KyomaHooin/Wireshield/openscad/schema/bls.jpg

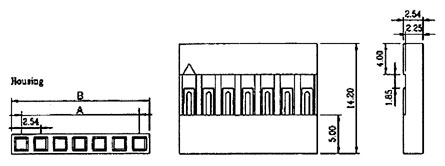
openscad/schema/bls.jpg
