KyomaHooin/Wireshield/openscad/schema/button.jpg

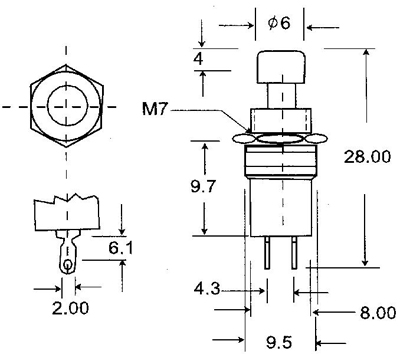
openscad/schema/button.jpg
