KyomaHooin/Wireshield/openscad/schema/idc.jpg

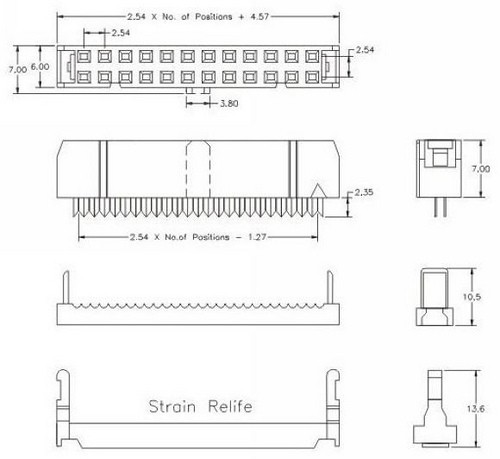
openscad/schema/idc.jpg
