KyomaHooin/Wireshield/openscad/schema/jack.jpg

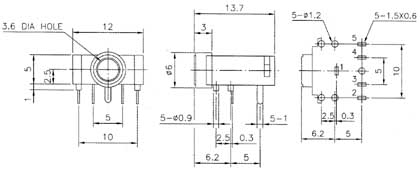
openscad/schema/jack.jpg
