KyomaHooin/Wireshield/openscad/schema/pls.jpg

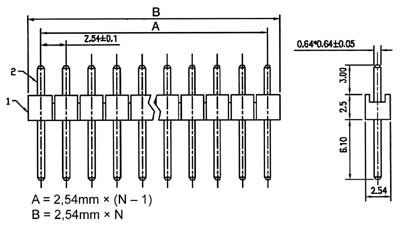
openscad/schema/pls.jpg
