KyomaHooin/Wireshield/openscad/schema/TFT.jpg

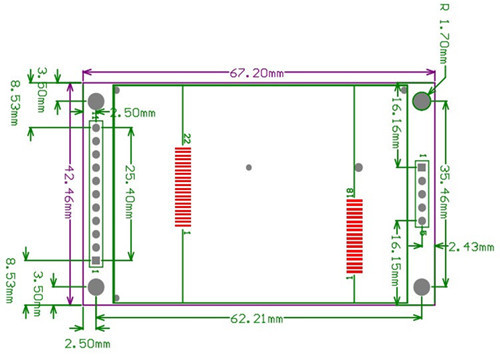
openscad/schema/TFT.jpg
