KyomaHooin/Wireshield/photo/IMG_20170406_092021.jpg

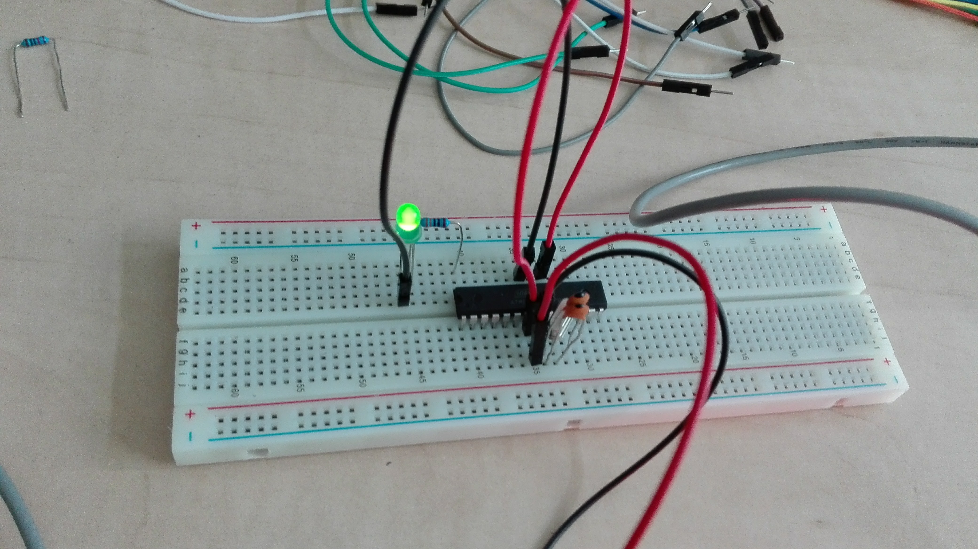
photo/IMG_20170406_092021.jpg
