KyomaHooin/Wireshield/photo/IMG_20170406_093931.jpg

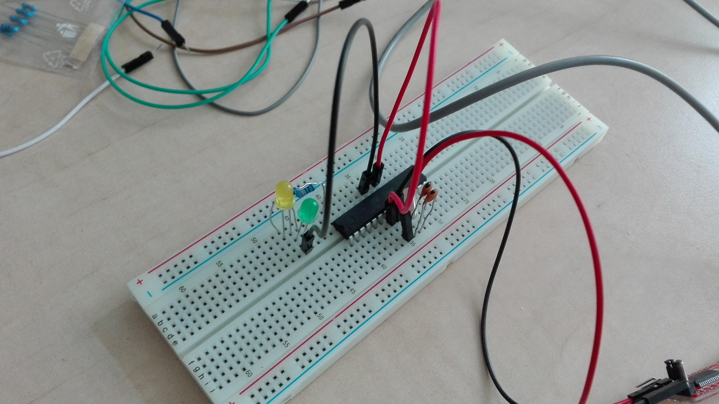
photo/IMG_20170406_093931.jpg
