KyomaHooin/Wireshield/photo/IMG_20170407_105513.jpg

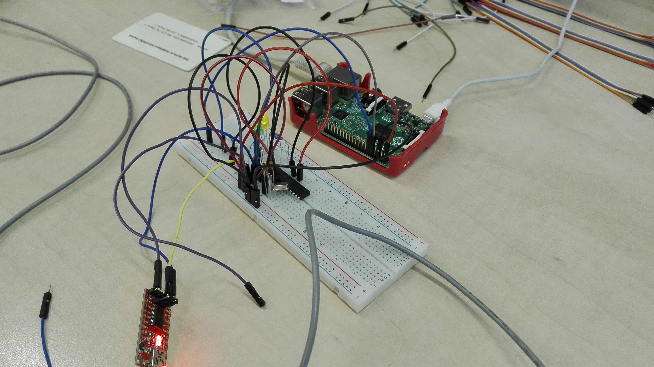
photo/IMG_20170407_105513.jpg
