KyomaHooin/Wireshield/photo/IMG_20170412_122922.jpg

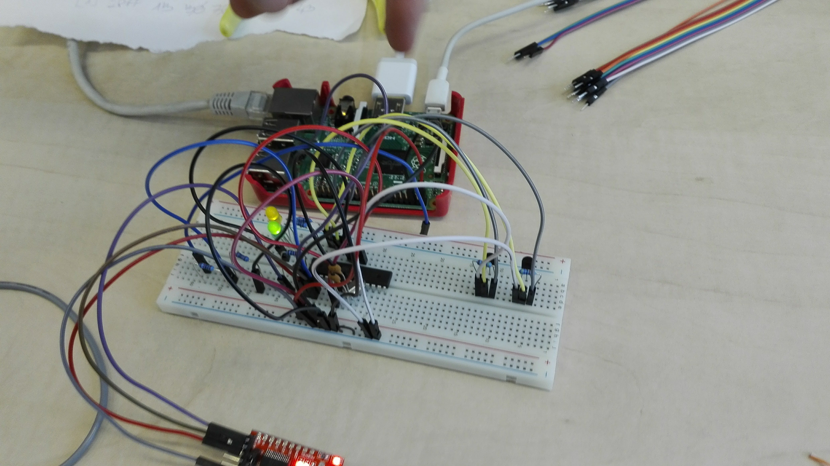
photo/IMG_20170412_122922.jpg
