KyomaHooin/Wireshield/photo/IMG_20170419_115917.jpg

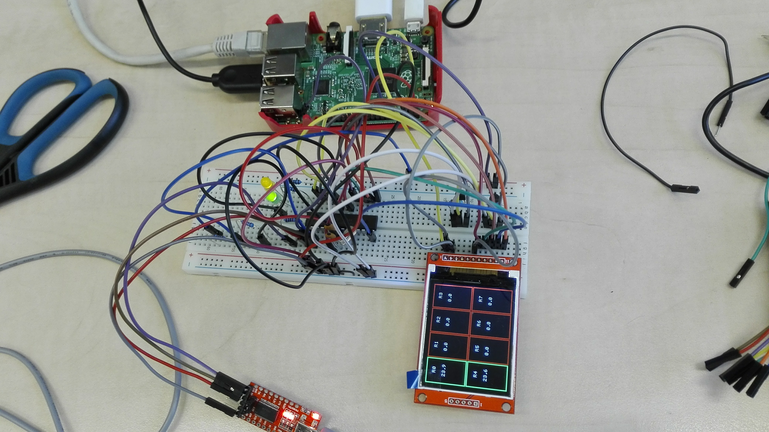
photo/IMG_20170419_115917.jpg
