KyomaHooin/Wireshield/photo/IMG_20170502_114444.jpg

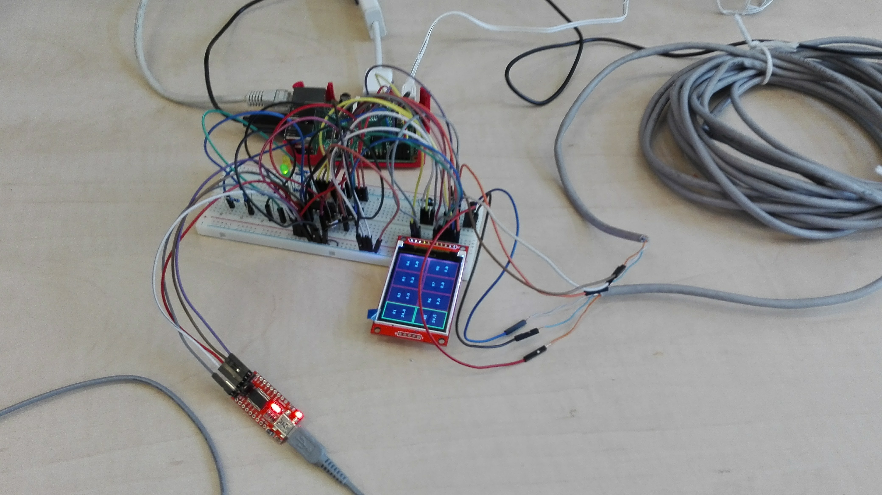
photo/IMG_20170502_114444.jpg
