KyomaHooin/Wireshield/photo/IMG_20170718_132216.jpg

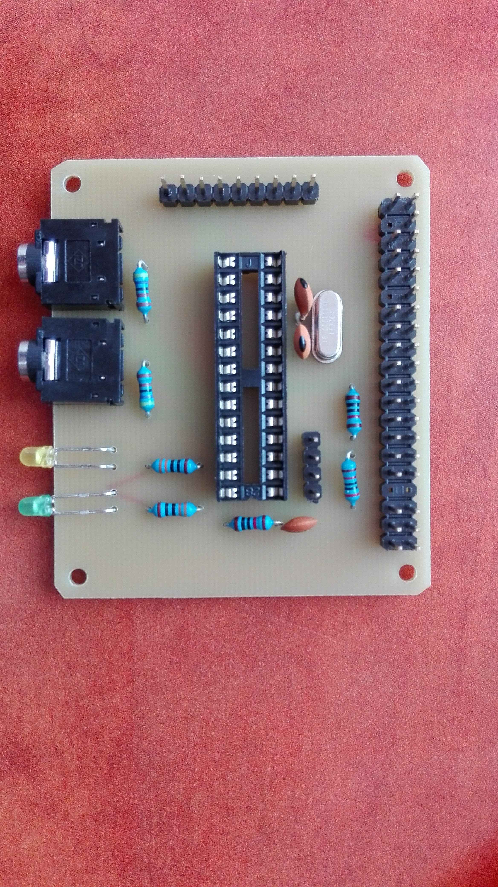
photo/IMG_20170718_132216.jpg
