KyomaHooin/Wireshield/photo/IMG_20170807_113755.jpg

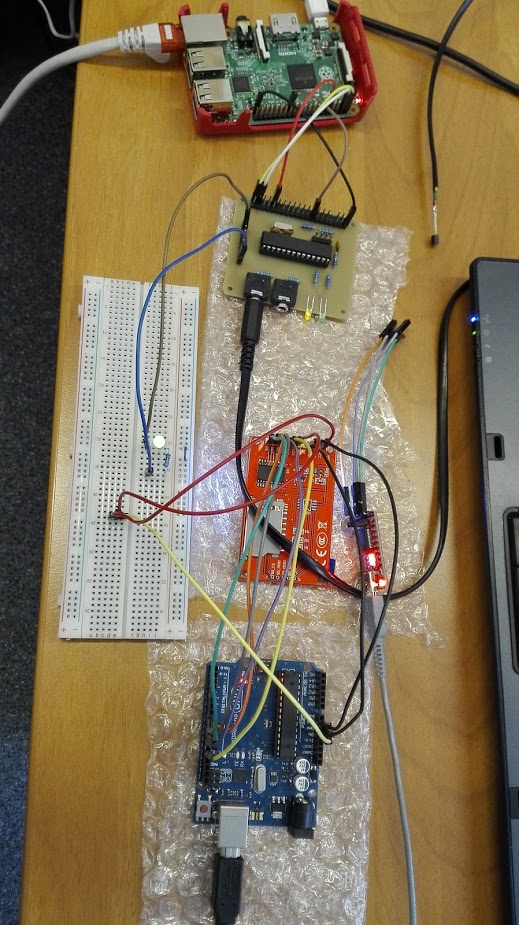
photo/IMG_20170807_113755.jpg
