KyomaHooin/Wireshield/photo/IMG_20170830_094421.jpg

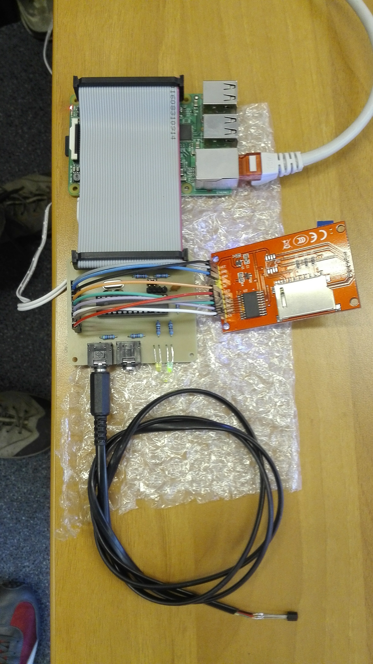
photo/IMG_20170830_094421.jpg
