KyomaHooin/Wireshield/photo/IMG_20170830_094432.jpg

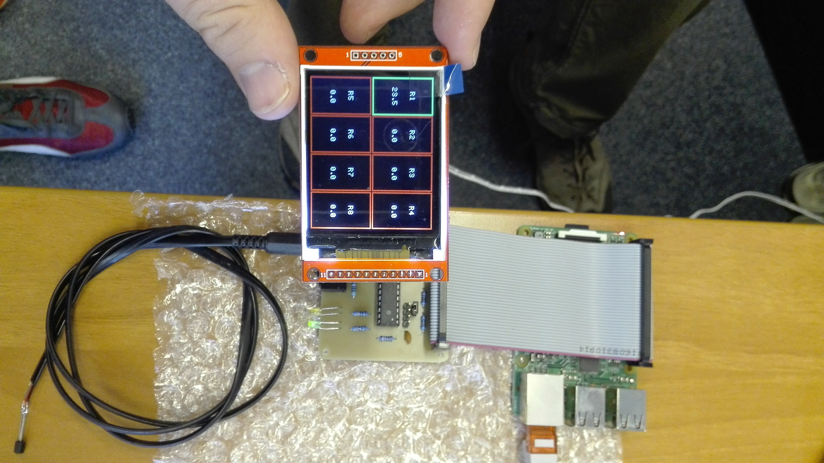
photo/IMG_20170830_094432.jpg
