KyomaHooin/Wireshield/photo/IMG_20180214_163721.jpg

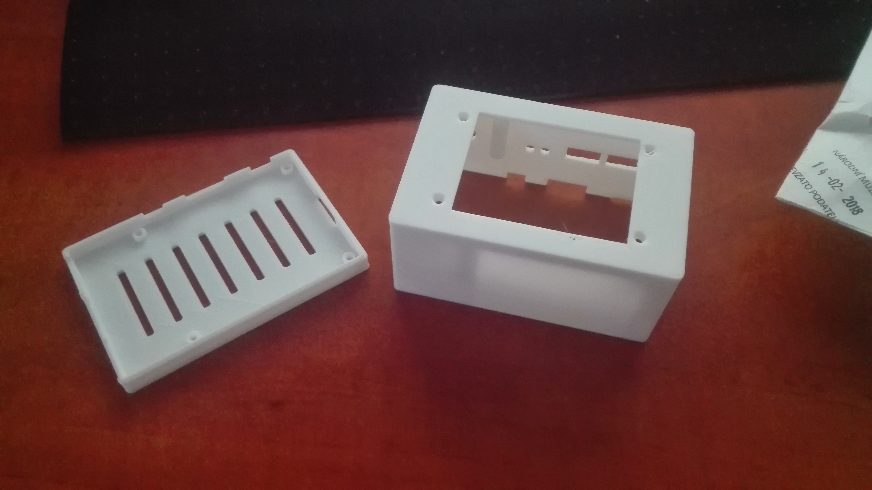
photo/IMG_20180214_163721.jpg
