KyomaHooin/Wireshield/photo/IMG_20180219_162749.jpg

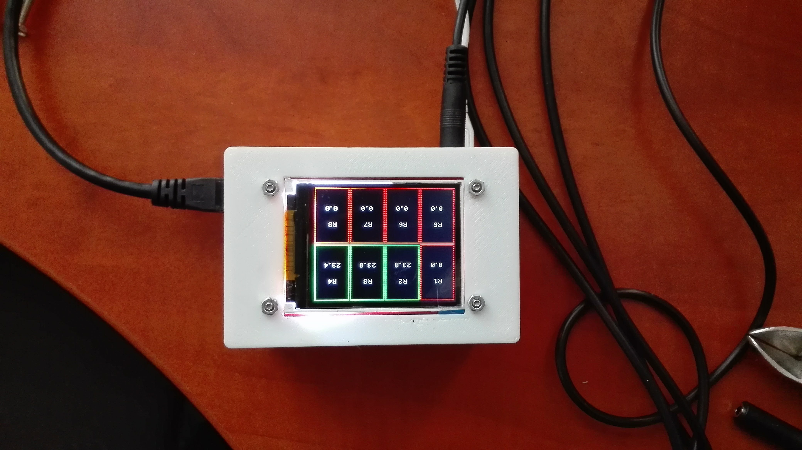
photo/IMG_20180219_162749.jpg
