KyomaHooin/Wireshield/photo/IMG_20180219_162757.jpg

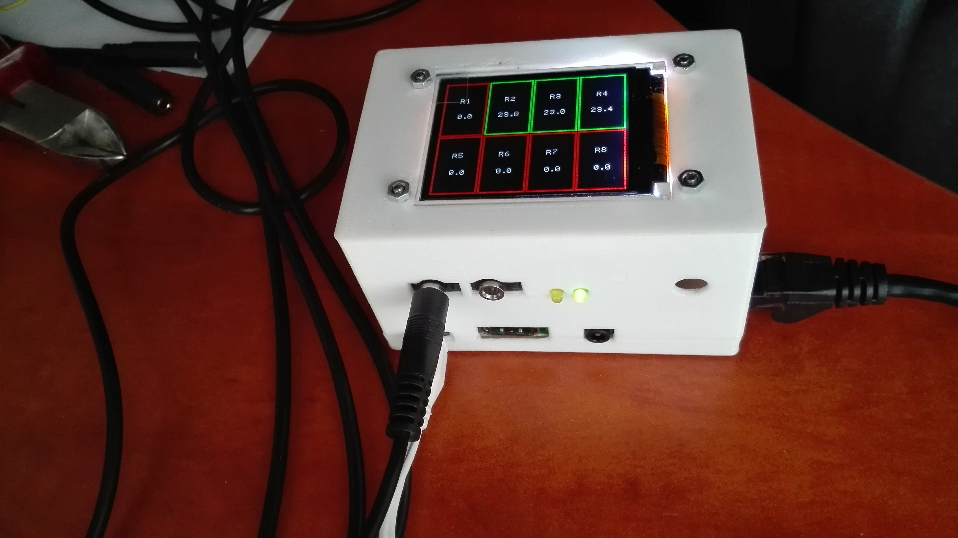
photo/IMG_20180219_162757.jpg
