KyomaHooin/Wireshield/photo/IMG_20180220_111004.jpg

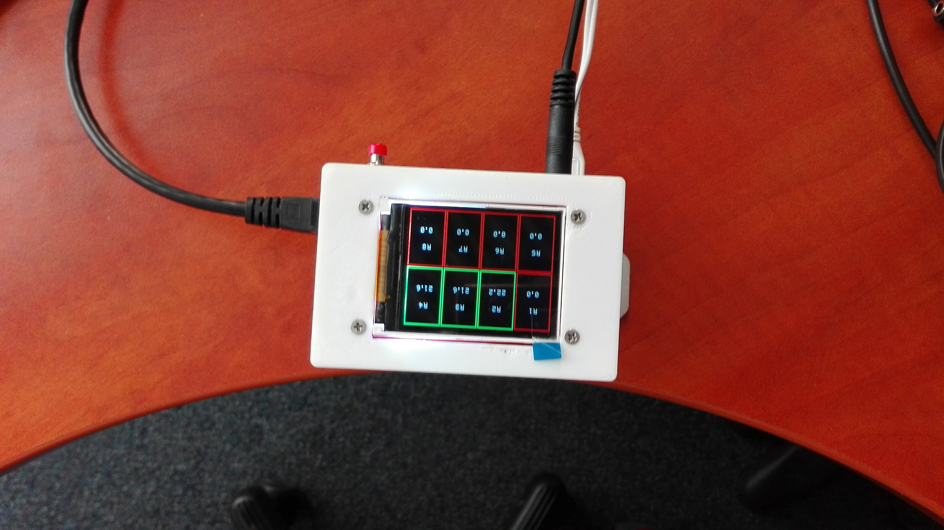
photo/IMG_20180220_111004.jpg
