KyomaHooin/Wireshield/photo/IMG_20180220_111011.jpg

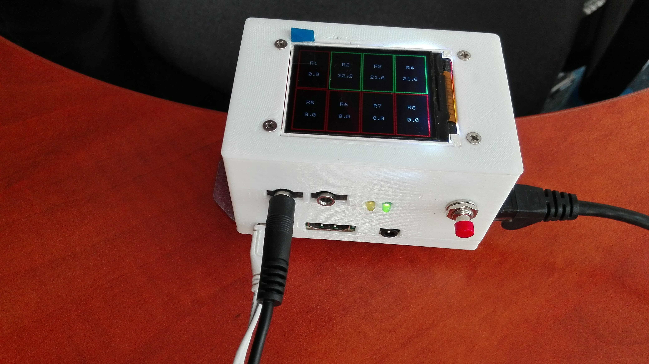
photo/IMG_20180220_111011.jpg
