KyomaHooin/Wireshield/photo/IMG_20180412_110601.jpg

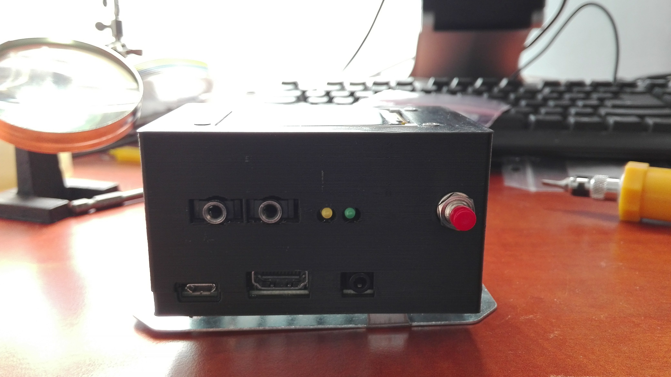
photo/IMG_20180412_110601.jpg
