KyomaHooin/Wireshield/photo/IMG_20180412_110608.jpg

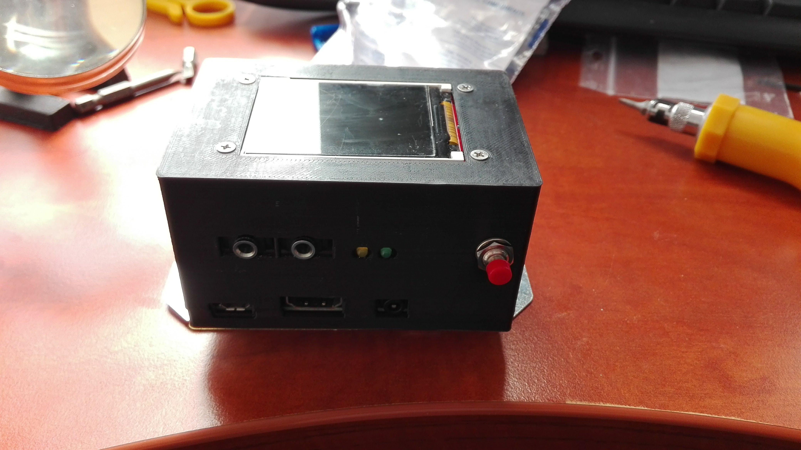
photo/IMG_20180412_110608.jpg
